The-XOR/CPUMeter/schema.kicad_sch

## KiCad design schema.kicad_sch (2025-05-10)

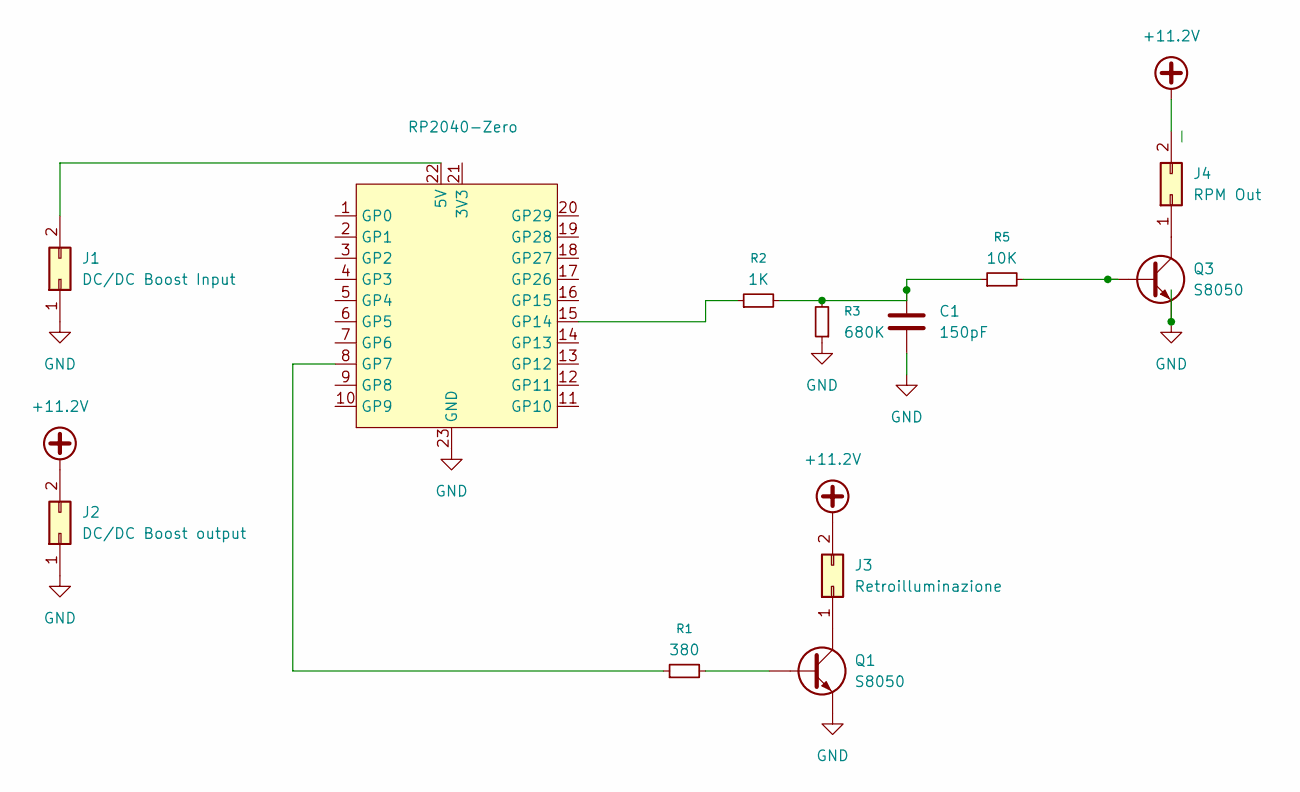
[picture p2: schematic schema.kicad_sch]

Parts:
C1: 150pF; C_Axial_L3.8mm_D2.6mm_P7.50mm_Horizontal
J1: DC/DC Boost Input; PinSocket_2x01_P2.54mm_Vertical
J2: DC/DC Boost output; PinSocket_2x01_P2.54mm_Vertical
J3: Retroilluminazione; PinSocket_2x01_P2.54mm_Vertical
J4: RPM Out; PinSocket_2x01_P2.54mm_Vertical
Q1, Q3: S8050; TO-92S
R1: 380; R_Axial_DIN0204_L3.6mm_D1.6mm_P5.08mm_Horizontal
R2: 1K; R_Axial_DIN0204_L3.6mm_D1.6mm_P5.08mm_Horizontal
R3: 680K; R_Axial_DIN0204_L3.6mm_D1.6mm_P5.08mm_Horizontal
R5: 10K; R_Axial_DIN0204_L3.6mm_D1.6mm_P5.08mm_Horizontal
RZ1: RP2040-Zero

Connections:
+11.2V: J2.2, J3.2, J4.2
GND: C1.2, J1.1, J2.1, Q1.1 (E), Q3.1 (E), R3.1, RZ1.23 (GND)
unnamed: C1.1, R2.2, R3.2, R5.1
unnamed: J1.2, RZ1.22 (5V)
unnamed: J3.1, Q1.3 (C)
unnamed: J4.1, Q3.3 (C)
unnamed: Q1.2 (B), R1.2
unnamed: Q3.2 (B), R5.2
unnamed: R1.1, RZ1.8 (GP7)
unnamed: R2.1, RZ1.15 (GP14)
